vanpit/JoyMegaAvr3/Pictures/20260628_172823.jpg

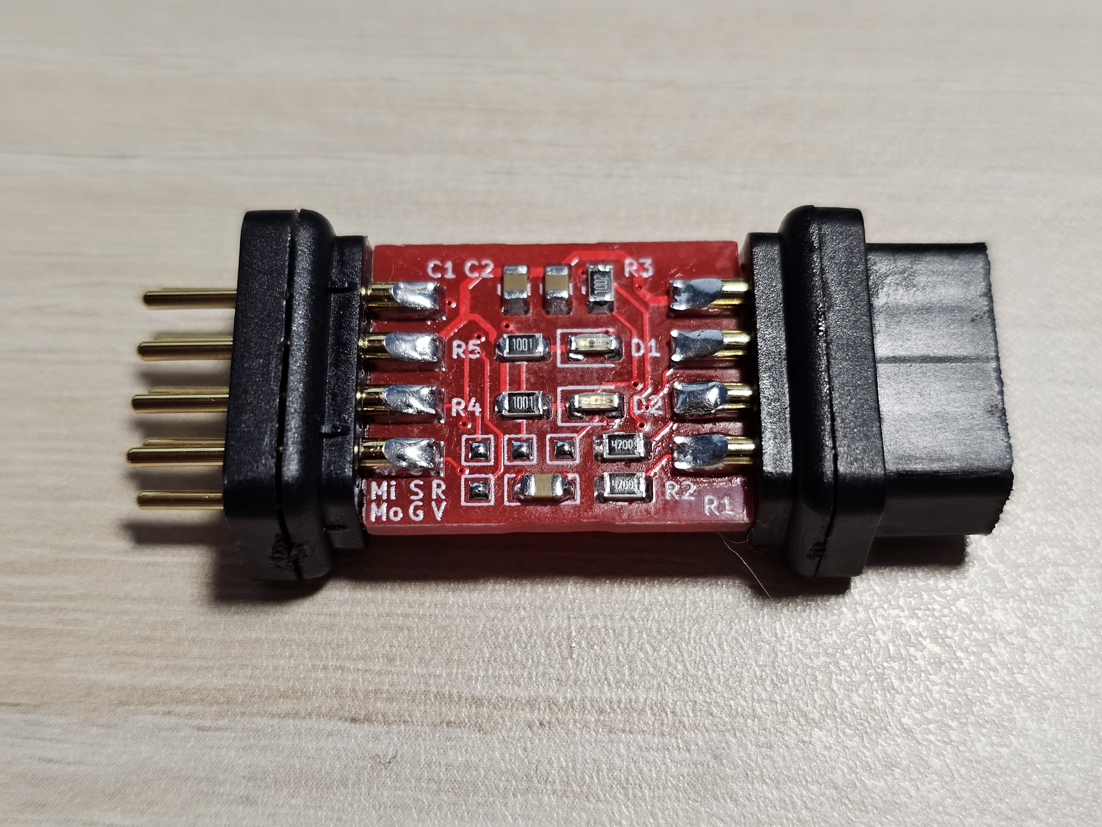
Pictures/20260628_172823.jpg
