vanpit/JoyMegaAvr3/Pictures/20260628_172921.jpg

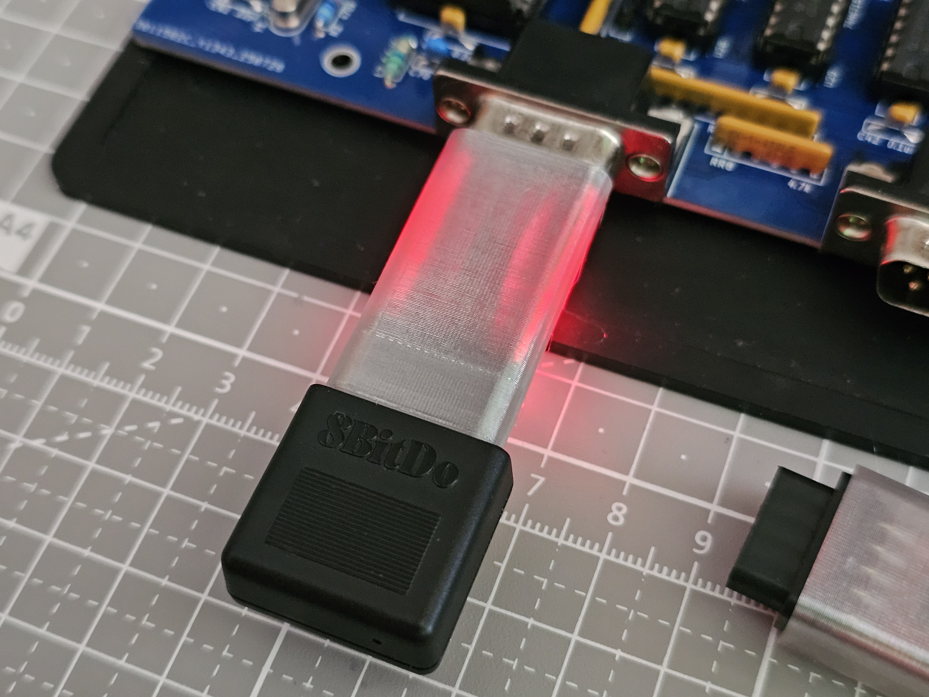
Pictures/20260628_172921.jpg
